UncleRus/EvLamp/main/effect.c

#include "effect.h"
#include <nvs.h>
#include "settings.h"
#include "surface.h"
#include "lib8tion.h"

////////////////////////////////////////////////////////////////////////////////

#include "effects/crazybees.h"
#include "effects/dna.h"
#include "effects/fire.h"
#include "effects/lamp.h"
#include "effects/lava.h"
#include "effects/matrix.h"
#include "effects/plasma_waves.h"
#include "effects/rain.h"
#include "effects/rainbow.h"
#include "effects/rays.h"
#include "effects/sparkles.h"
#include "effects/waterfall.h"
#include "effects/metaballs.h"
#include "effects/water.h"
#include "effects/holiday.h"
#include "effects/hoop.h"
#include "effects/twister.h"
#include "effects/flower.h"
#include "effects/polar_lights.h"
#include "effects/gif.h"
#include "effects/relax.h"
#include "effects/wheel.h"
#include "effects/peacock.h"
#include "effects/diagonals.h"
#include "effects/whirls.h"
#include "effects/sun.h"
#include "effects/spaceships.h"
#include "effects/fireflies.h"
#include "effects/tunnel.h"
#include "effects/dunes.h"
#include "effects/octopus.h"
#include "effects/nuclear.h"

const effect_descriptor_t effects[] = {
    DESCR_EFFECT_LAMP,
    DESCR_EFFECT_FIRE,
    DESCR_EFFECT_SPARKLES,
    DESCR_EFFECT_LAVA,
    DESCR_EFFECT_WATERFALL,
    DESCR_EFFECT_PLASMA_WAVES,
    DESCR_EFFECT_DNA,
    DESCR_EFFECT_MATRIX,
    DESCR_EFFECT_CRAZYBEES,
    DESCR_EFFECT_RAIN,
    DESCR_EFFECT_RAINBOW,
    DESCR_EFFECT_RAYS,
    DESCR_EFFECT_METABALLS,
    DESCR_EFFECT_WATER,
    DESCR_EFFECT_HOLIDAY,
    DESCR_EFFECT_HOOP,
    DESCR_EFFECT_TWISTER,
    DESCR_EFFECT_FLOWER,
    DESCR_EFFECT_POLAR_LIGHTS,
    DESCR_EFFECT_GIF,
    DESCR_EFFECT_RELAX,
    DESCR_EFFECT_WHEEL,
    DESCR_EFFECT_PEACOCK,
    DESCR_EFFECT_DIAGONALS,
    DESCR_EFFECT_WHIRLS,
    DESCR_EFFECT_SUN,
    DESCR_EFFECT_SPACESHIPS,
    DESCR_EFFECT_FIREFLIES,
    DESCR_EFFECT_TUNNEL,
    DESCR_EFFECT_DUNES,
    DESCR_EFFECT_OCTOPUS,
    DESCR_EFFECT_NUCLEAR,
};

const size_t effects_count = sizeof(effects) / sizeof(effect_descriptor_t);

#define PARAM(effect, param) effects[(effect)].params[(param)]

////////////////////////////////////////////////////////////////////////////////

static const char *STORAGE_PARAMS_NAME = "effects";
static const char *NVS_KEY_FMT = "e%04x:p%04x";

esp_err_t effects_reset()
{
    // FIXME not effective
    for (size_t e = 0; e < effects_count; e++)
        for (size_t p = 0; p < effects[e].params_count; p++)
            CHECK_LOGE(effect_param_set(e, p, PARAM(e, p).def),
                    "Could not set %s.%s to %d", effects[e].name, PARAM(e, p).name, PARAM(e, p).def);

    ESP_LOGW(TAG, "Effect parameters have been reset to defaults");

    return ESP_OK;
}

esp_err_t effect_param_set(size_t effect, size_t param, uint8_t value)
{
    CHECK_ARG(effect < effects_count
            && param < effects[effect].params_count
            && value >= PARAM(effect, param).min
            && value <= PARAM(effect, param).max);

    if (PARAM(effect, param).value == value)
        return ESP_OK;

    nvs_handle_t nvs;
    CHECK_LOGE(nvs_open(STORAGE_PARAMS_NAME, NVS_READWRITE, &nvs),
            "Could not open NVS storage '%s'", STORAGE_PARAMS_NAME);
    char key[NVS_KEY_NAME_MAX_SIZE];
    snprintf(key, sizeof(key), NVS_KEY_FMT, effect, param);
    nvs_set_u8(nvs, key, value);
    nvs_close(nvs);

    ESP_LOGI(TAG, "'%s':'%s' = %d", effects[effect].name, PARAM(effect, param).name, value);

    PARAM(effect, param).value = value;
    if (effect == vol_settings.effect)
        CHECK_LOGE(surface_prepare_effect(effect), "Could not prepare effect");

    return ESP_OK;
}

static esp_err_t effect_params_load()
{
    char key[NVS_KEY_NAME_MAX_SIZE];
    uint8_t val;

    nvs_handle_t nvs;
    CHECK_LOGE(nvs_open(STORAGE_PARAMS_NAME, NVS_READWRITE, &nvs),
            "Could not open NVS storage '%s'", STORAGE_PARAMS_NAME);

    // read effect params
    for (size_t e = 0; e < effects_count; e++)
    {
        ESP_LOGI(TAG, "Effect %d: '%s'", e, effects[e].name);
        for (size_t p = 0; p < effects[e].params_count; p++)
        {
            snprintf(key, sizeof(key), NVS_KEY_FMT, e, p);

            val = PARAM(e, p).def;
            esp_err_t res = nvs_get_u8(nvs, key, &val);
            if (res == ESP_ERR_NVS_NOT_FOUND || val < PARAM(e, p).min || val > PARAM(e, p).max)
            {
                val = PARAM(e, p).def;
                nvs_set_u8(nvs, key, val);
            }
            PARAM(e, p).value = val;

            ESP_LOGI(TAG, "    %s: %d (min %d, max %d, def %d)",
                    PARAM(e, p).name, PARAM(e, p).value, PARAM(e, p).min, PARAM(e, p).max, PARAM(e, p).def);
        }
    }
    nvs_close(nvs);

    ESP_LOGI(TAG, "Effect parameters loaded");

    return ESP_OK;
}

esp_err_t effects_init()
{
    esp_err_t res = effect_params_load();
    if (res != ESP_OK)
        res = effects_reset();

    random16_set_seed(esp_cpu_get_cycle_count() & 0xffff);

    return res;
}
